Jodaille/LyceeDesAndaines/JaugePluieInterruption/Contact_removed_cutted.jpg

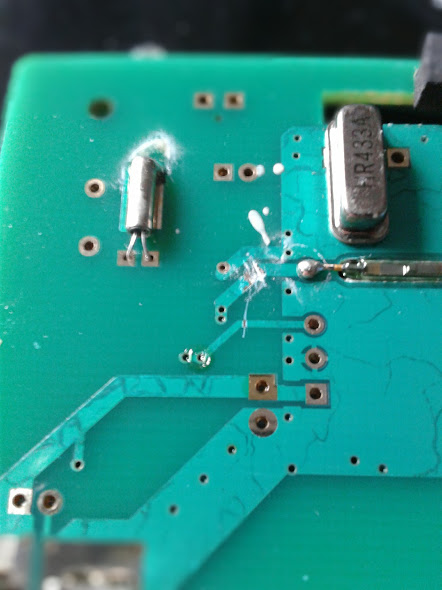
JaugePluieInterruption/Contact_removed_cutted.jpg
