Jodaille/LyceeDesAndaines/ReceptionBarometre433mhz/ReceptionBarometre433mhz.ino

/**
 * credits:
 * https://skyduino.wordpress.com/2011/12/29/tutoriel-arduino-et-emetteurrecepteur-433mhz-virtualwire/
 */

#include <VirtualWire.h> // inclusion de la librairie VirtualWire

#include "BMP280.h" // https://github.com/mahfuz195/BMP280-Arduino-Library
#include "Wire.h"
#define P0 1013.25
BMP280 bmp;

// reception par defaut sur pinout 11 (DATA)

struct data_t {
    int temperature;
    int humidity;
    byte voltage;
    byte id;
    }; // user defined data structure
data_t data; // define a variable with that structure

void setup() // Fonction setup()
{
    Serial.begin(9600); // Initialisation du port série pour avoir un retour sur le serial monitor
    Serial.println("Reception VirtualWire"); // Petit message de bienvenue

    vw_setup(2000); // initialisation de la librairie VirtualWire à 2000 bauds (note: je n'utilise pas la broche PTT)
    vw_rx_start();  // Activation de la partie réception de la librairie VirtualWire

  if(bmp.begin()){
    bmp.setOversampling(4);
  }

}

void loop() // Fonction loop()
{
    uint8_t buf[VW_MAX_MESSAGE_LEN]; // Tableau qui va contenir le message reçu (de taille maximum VW_MAX_MESSAGE_LEN)
    uint8_t buflen = VW_MAX_MESSAGE_LEN; // Taille maximum de notre tableau

    // REMARQUE ULTRA IMPORTANTE :
    //   Par le passé ces deux lignes se trouvaient en "haut de programme", c'était donc des variables globales.
    //   Elles ne doivent PAS être globales, c'est très important !
    //
    //    Pourquoi ?
    //    C'est très simple. Posez vous la question suivante : que vaut "buflen" si la réception d'un message échoue,
    //    où qu'on reçoit un message de moins de VW_MAX_MESSAGE_LEN octets ?
    //    Au début "buflen" vaut VW_MAX_MESSAGE_LEN, mais après "buflen" vaudra une valeur < VW_MAX_MESSAGE_LEN.
    //    Et paf, la taille de votre buffer vient de diminuer pour la réception suivante, et ainsi de suite.

    if (vw_wait_rx_max(200)) // Si un message est reçu dans les 200ms qui viennent
    {
        if (vw_get_message(buf, &buflen)) // On copie le message, qu'il soit corrompu ou non
        {
            if (buflen == sizeof(data_t)){
                memcpy( &data, buf, sizeof(data));

                float temperature = data.temperature/(float)100;
                float humidity = data.humidity/(float)100;
                byte voltage = data.voltage;

                Serial.print("id=");
                Serial.print(data.id);

                Serial.print(";V=");
                Serial.print(voltage);

                Serial.print(";t1=");
                Serial.print(temperature);

                Serial.print(";h=");
                Serial.print(humidity, 2);

                double T,P;
                char result = bmp.startMeasurment();
                result = bmp.getTemperatureAndPressure(T,P);
                Serial.print(";Bt=");Serial.print(T,2); //temperature °C
                Serial.print(";P=");Serial.print(P,2);// pression mBar
                Serial.println("");


            }
        }
    }
}
